DevX-Dragon/DraX-Pad/Images/3D render .png

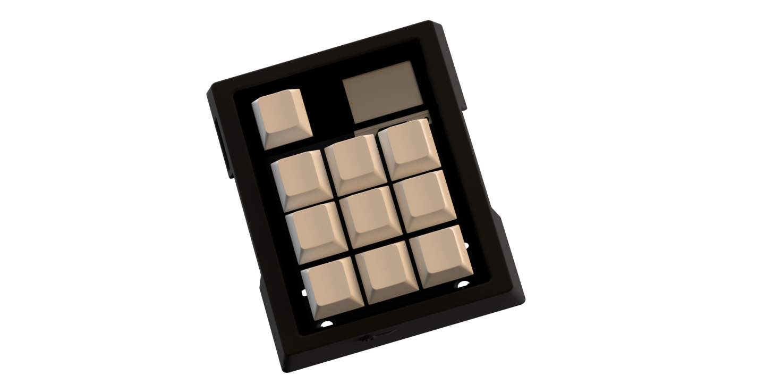
Images/3D render .png
