DevX-Dragon/DraX-Pad/Images/PCB 3D Back.png

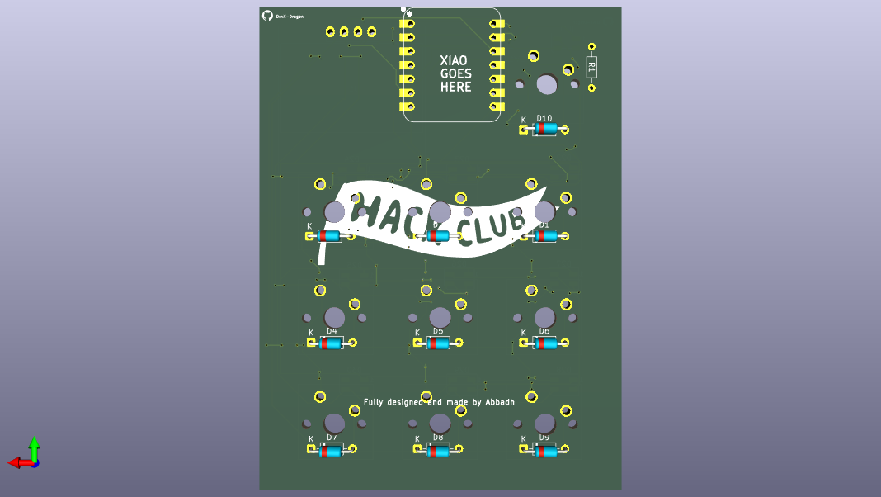
Images/PCB 3D Back.png
