DevX-Dragon/DraX-Pad/Images/plain-one.png

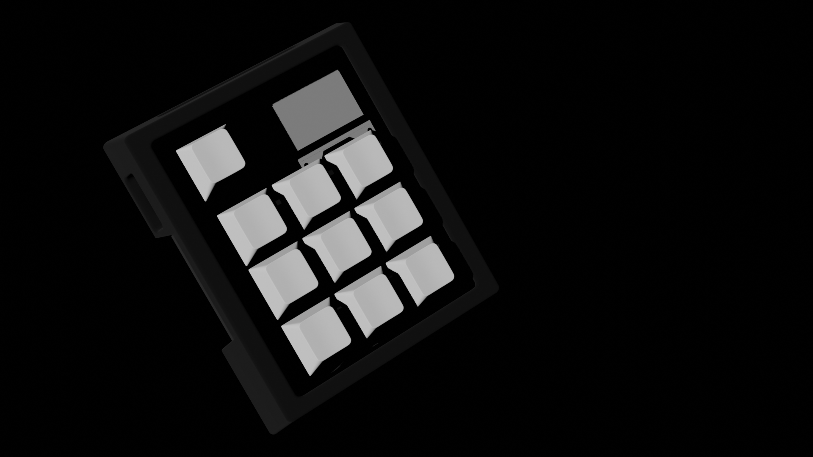
Images/plain-one.png
