DevX-Dragon/DraX-Pad/Images/render with PCB visible.png

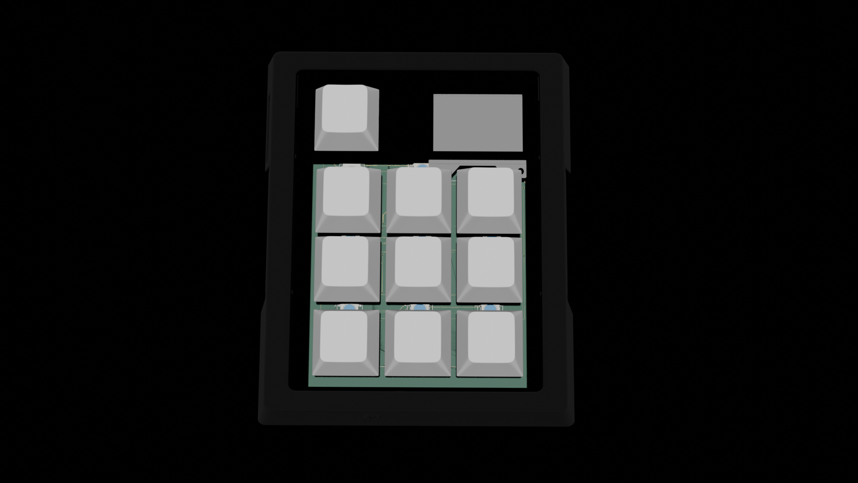
Images/render with PCB visible.png
